beniroquai/Opentrons-Microscope-Platereader/image.png

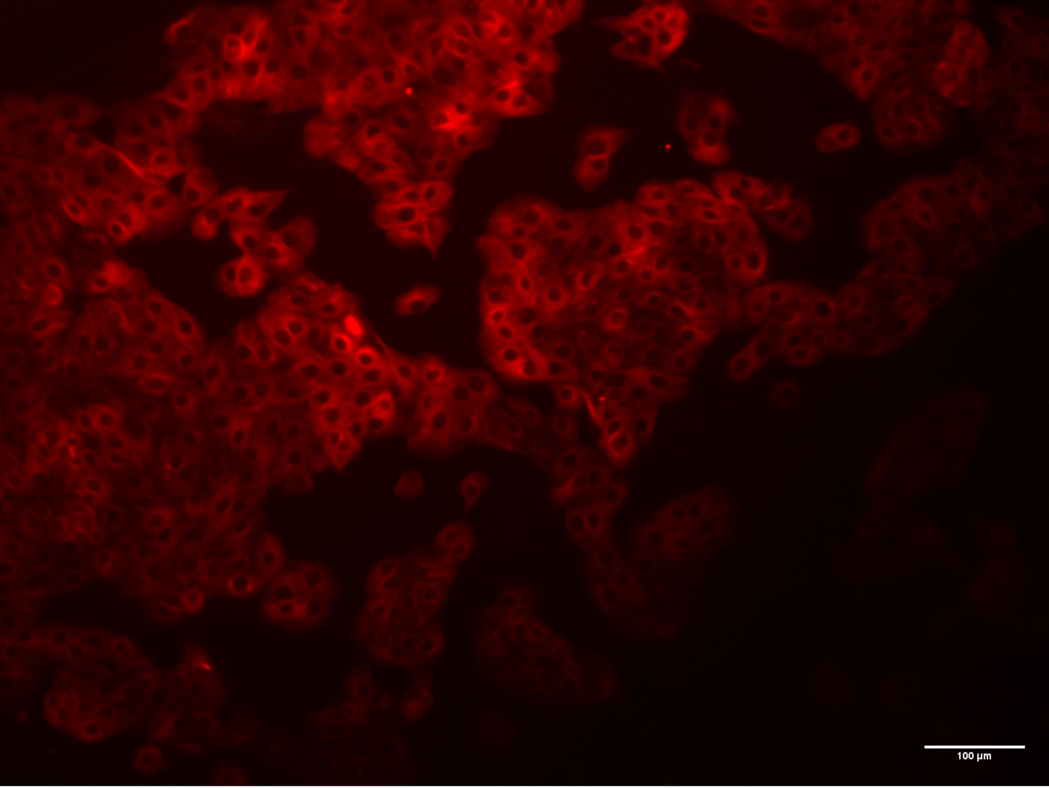
image.png
