beniroquai/Opentrons-Microscope-Platereader/IMAGES/FIG_Fluo_ring.jpg

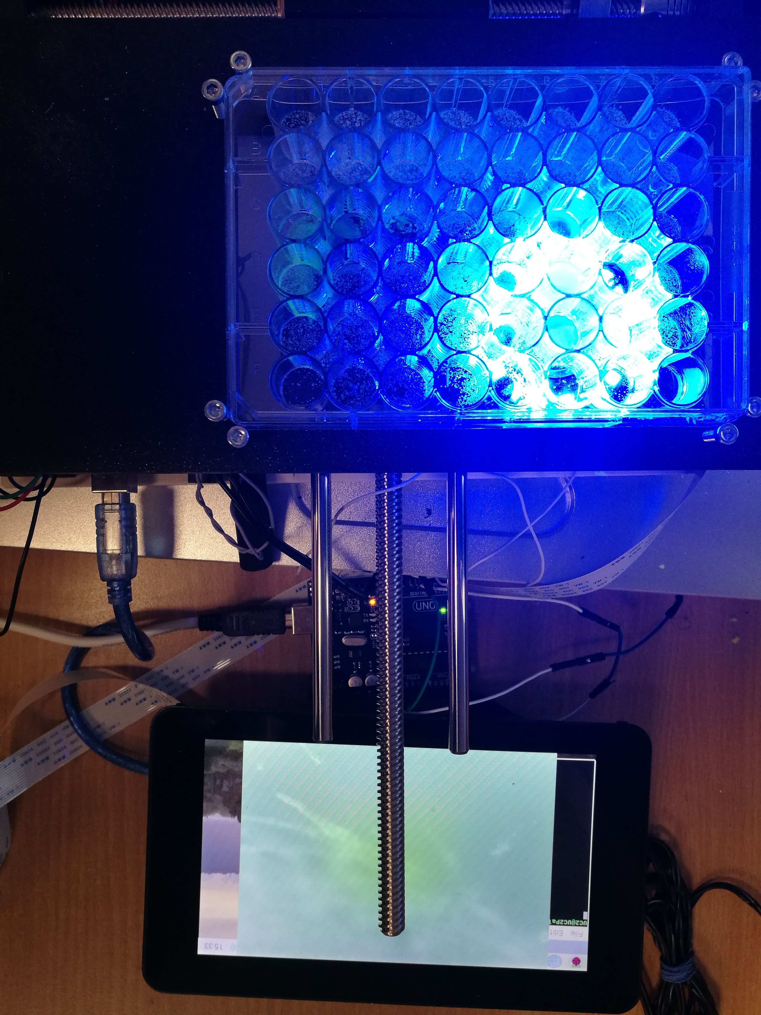
IMAGES/FIG_Fluo_ring.jpg
