beniroquai/Opentrons-Microscope-Platereader/IMAGES/laserpos.gif

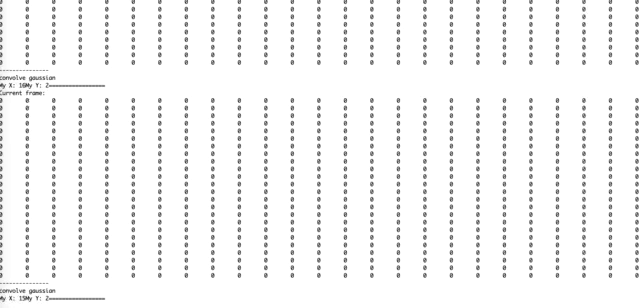
IMAGES/laserpos.gif
