beniroquai/Opentrons-Microscope-Platereader/IMAGES/Opentrons_6.jpg

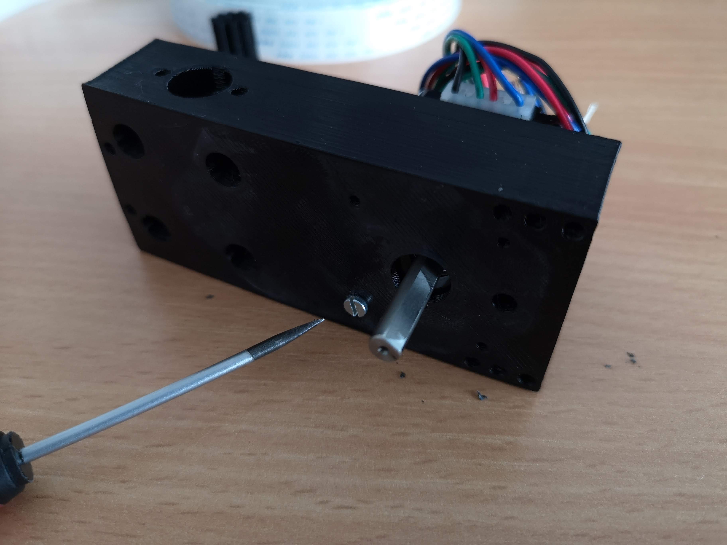
IMAGES/Opentrons_6.jpg
