beniroquai/Opentrons-Microscope-Platereader/IMAGES/Opentrons_70.jpg

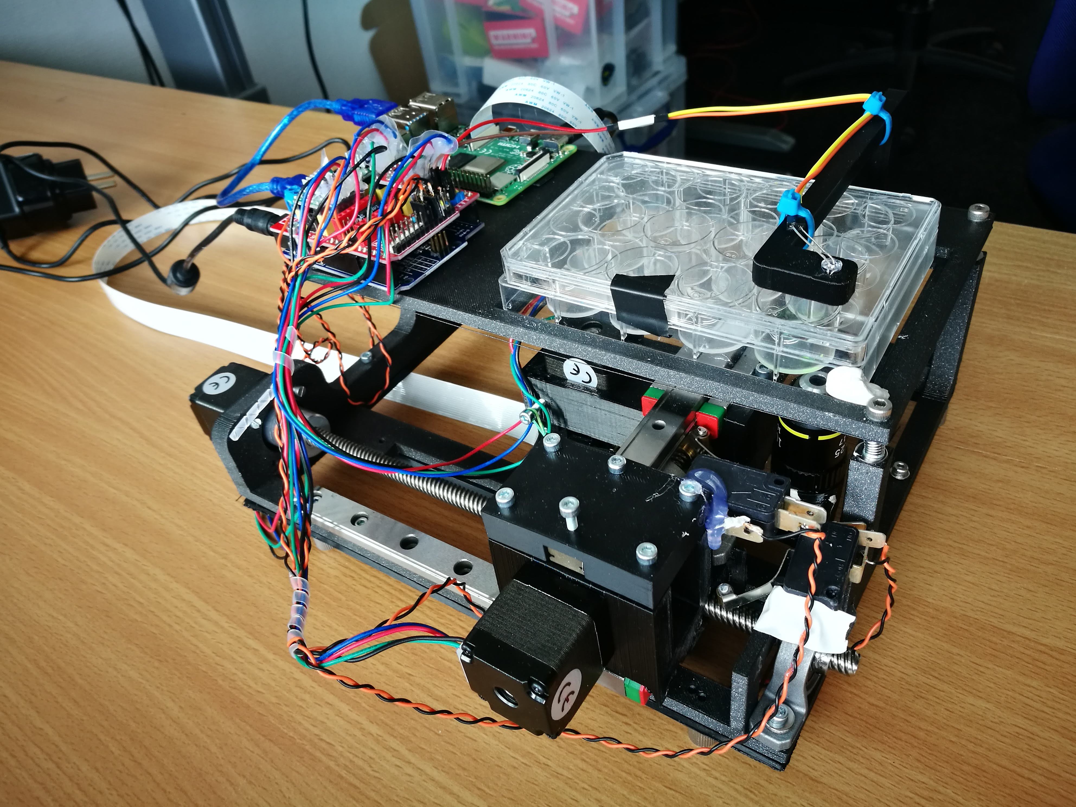
IMAGES/Opentrons_70.jpg
