beniroquai/Opentrons-Microscope-Platereader/IMAGES/Opentrons_71.jpg

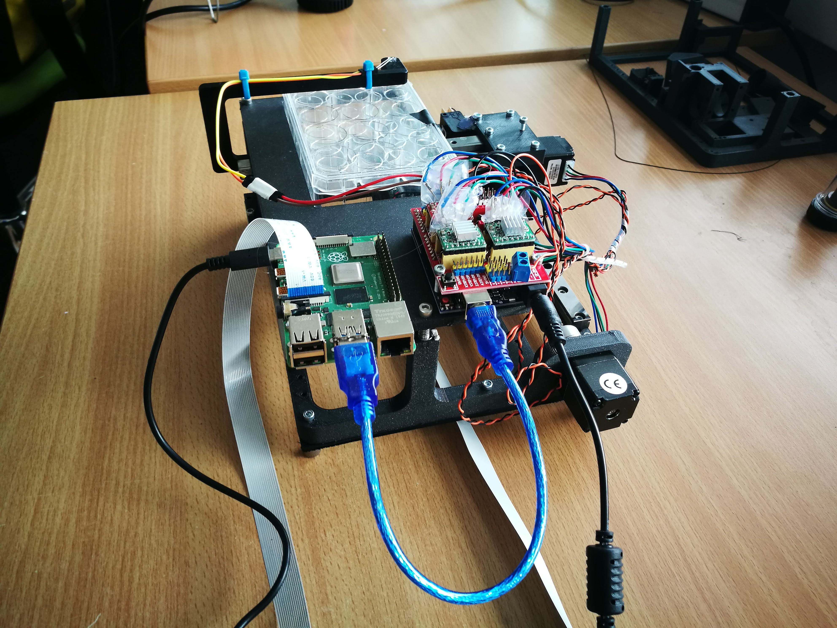
IMAGES/Opentrons_71.jpg
