beniroquai/Opentrons-Microscope-Platereader/IMAGES/Opentrons_72.jpg

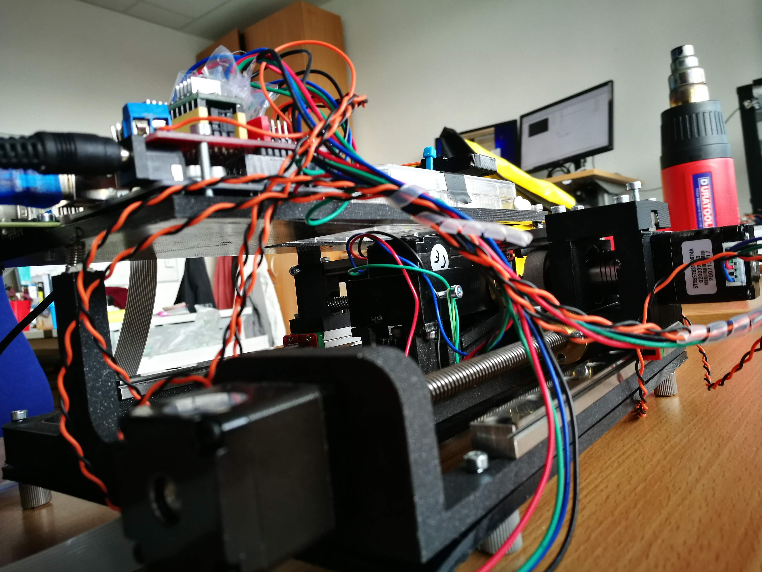
IMAGES/Opentrons_72.jpg
