beniroquai/Opentrons-Microscope-Platereader/IMAGES/Opentrons_73.jpg

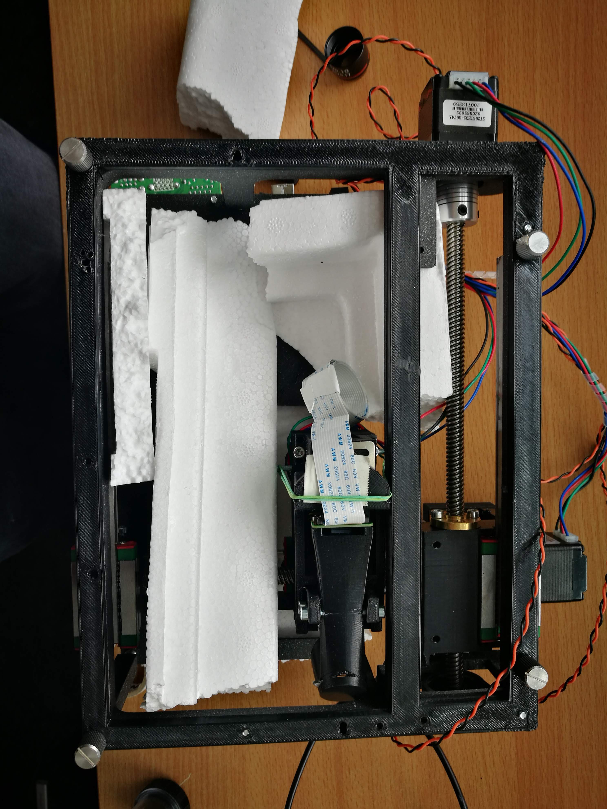
IMAGES/Opentrons_73.jpg
