beniroquai/Opentrons-Microscope-Platereader/IMAGES/Opentronsscope.png

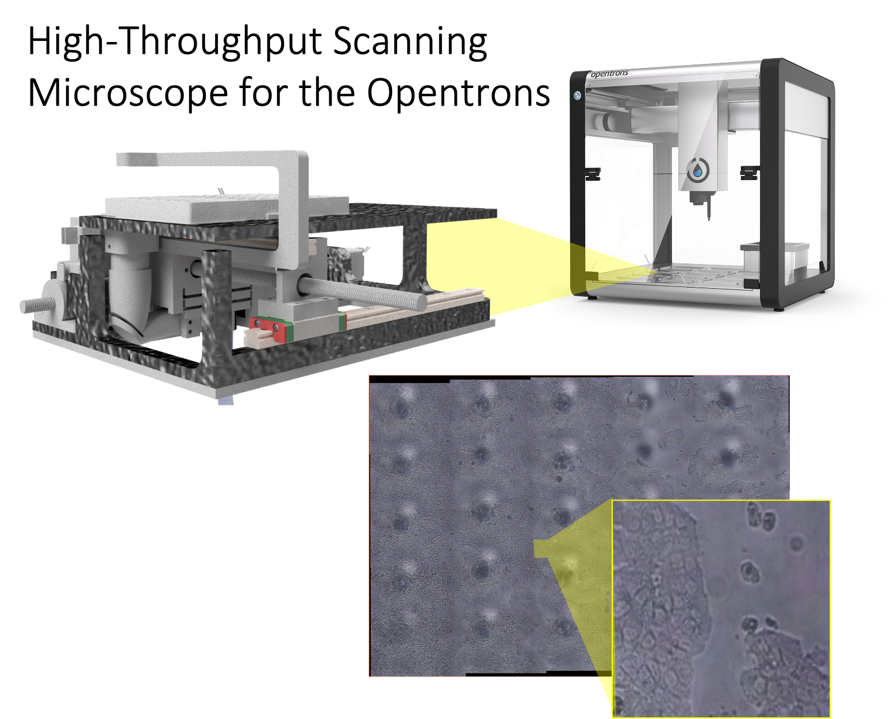
IMAGES/Opentronsscope.png
