beniroquai/Opentrons-Microscope-Platereader/IMAGES/OT_1.jpg

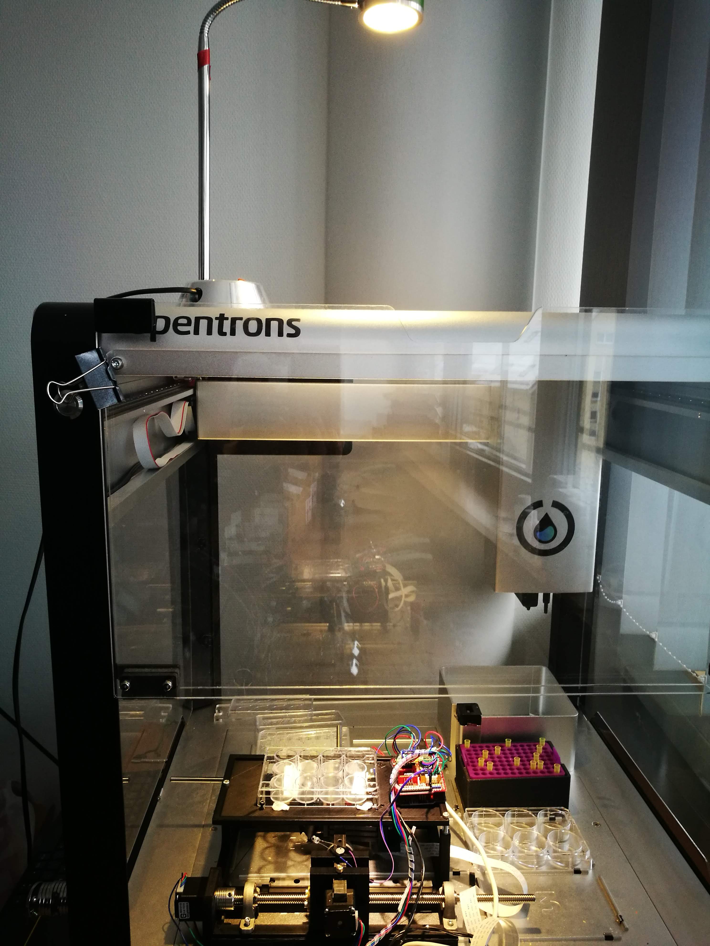
IMAGES/OT_1.jpg
