beniroquai/Opentrons-Microscope-Platereader/IMAGES/OT_2.jpg

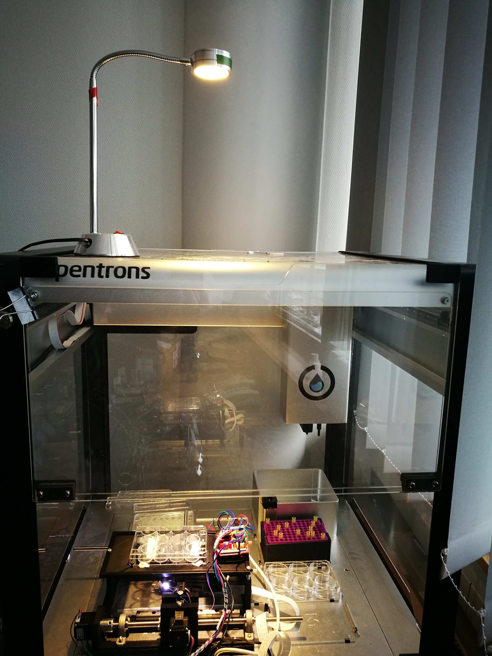
IMAGES/OT_2.jpg
