beniroquai/Opentrons-Microscope-Platereader/IMAGES/OT_3.jpg

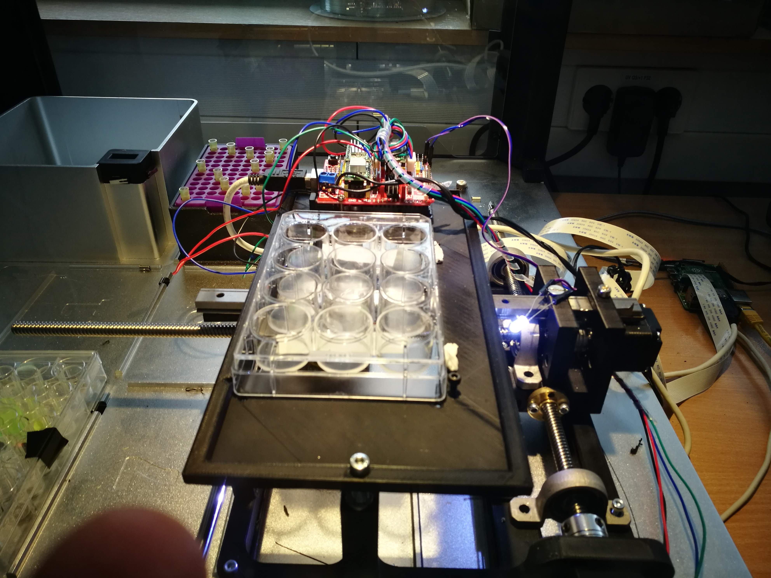
IMAGES/OT_3.jpg
