beniroquai/Opentrons-Microscope-Platereader/IMAGES/OT_4.jpg

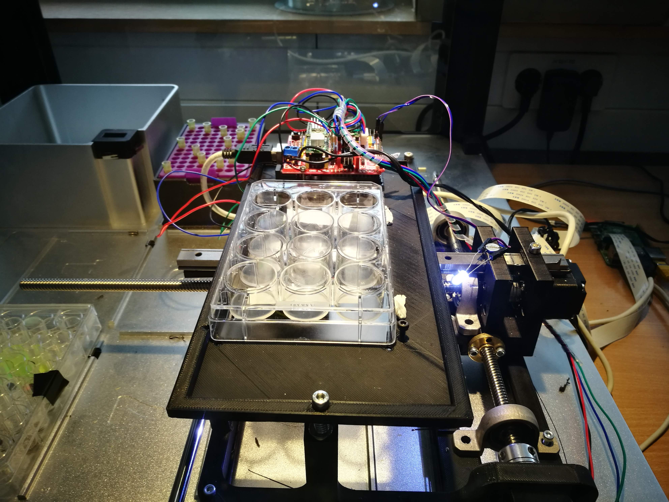
IMAGES/OT_4.jpg
