beniroquai/Opentrons-Microscope-Platereader/IMAGES/Spectrometer_Neopixel_ring_onlyBlue.PNG

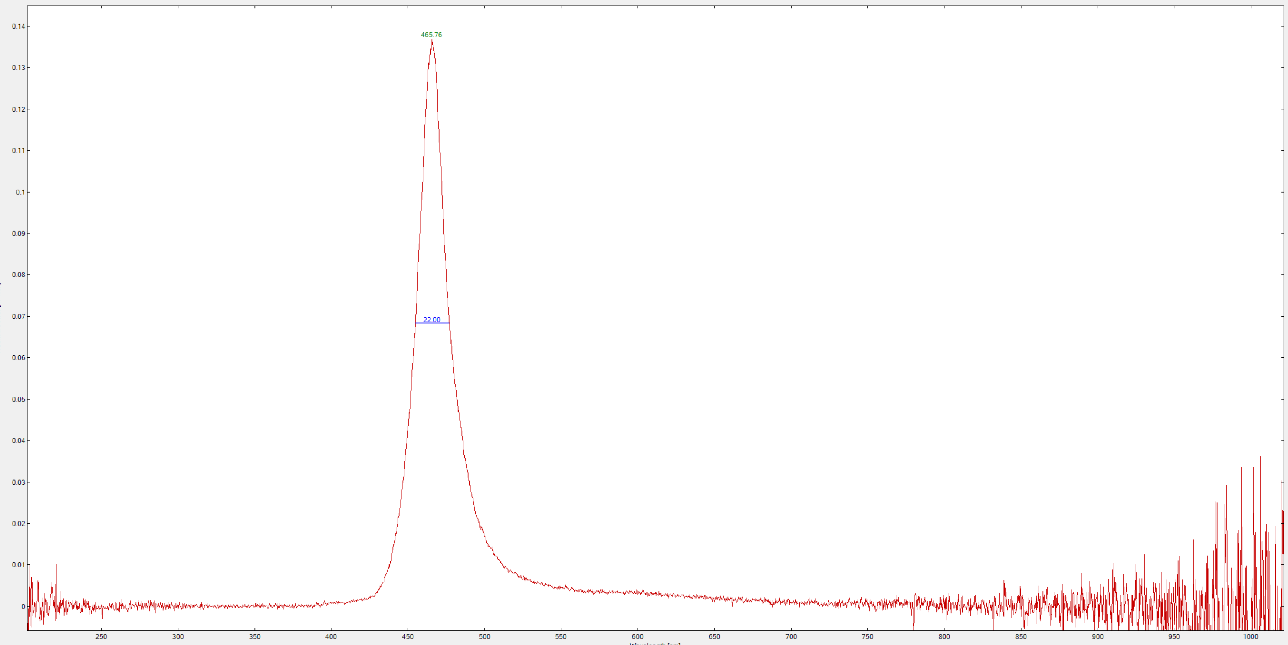
IMAGES/Spectrometer_Neopixel_ring_onlyBlue.PNG
