beniroquai/Opentrons-Microscope-Platereader/IMAGES/Stitch1.jpeg

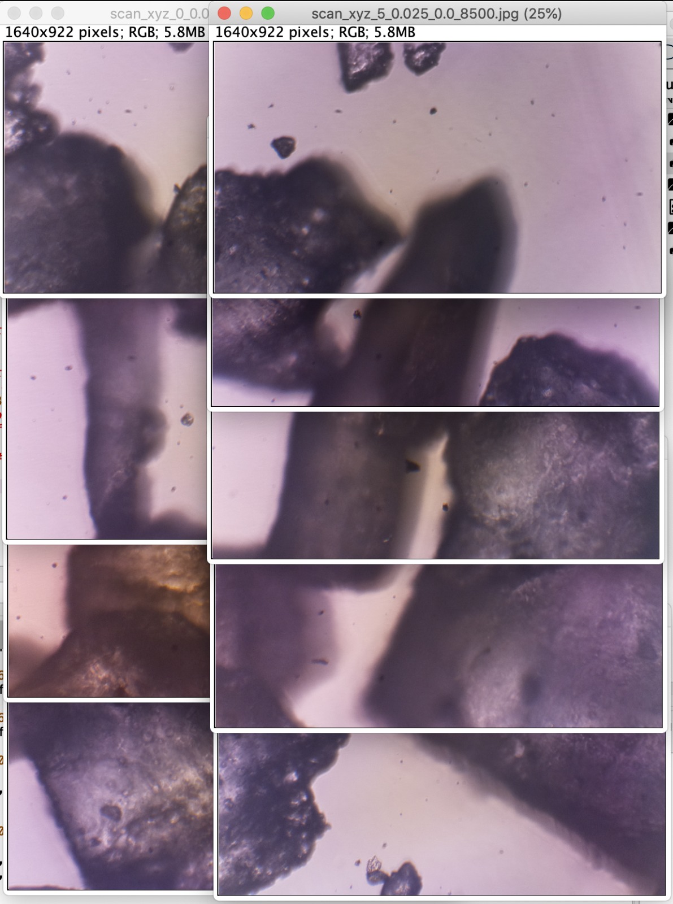
IMAGES/Stitch1.jpeg
