beniroquai/Opentrons-Microscope-Platereader/IMAGES/Z-Stack.gif

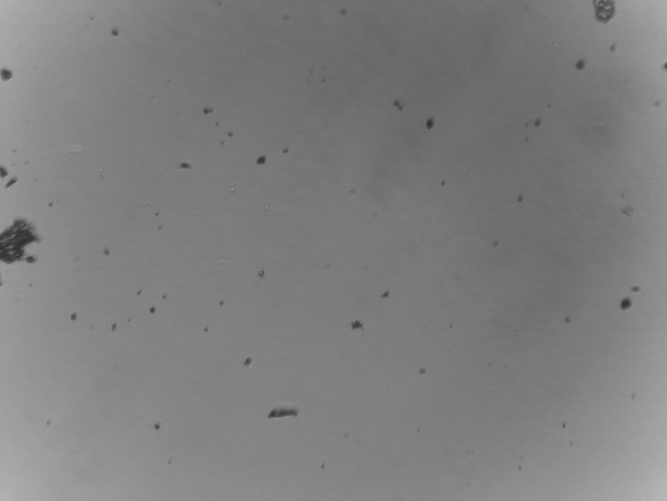
IMAGES/Z-Stack.gif
