beniroquai/Opentrons-Microscope-Platereader/INVENTOR/eppi.PNG

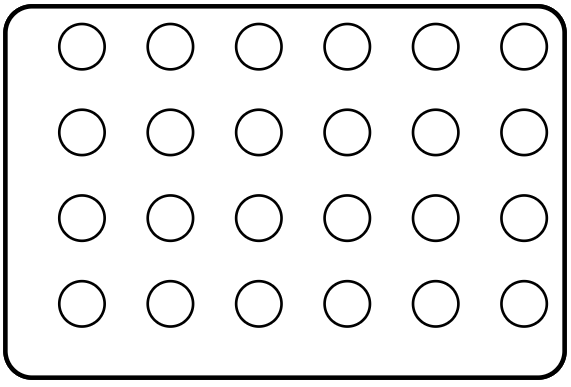
INVENTOR/eppi.PNG
