beniroquai/Opentrons-Microscope-Platereader/INVENTOR/IMG-20210314-WA0000.jpg

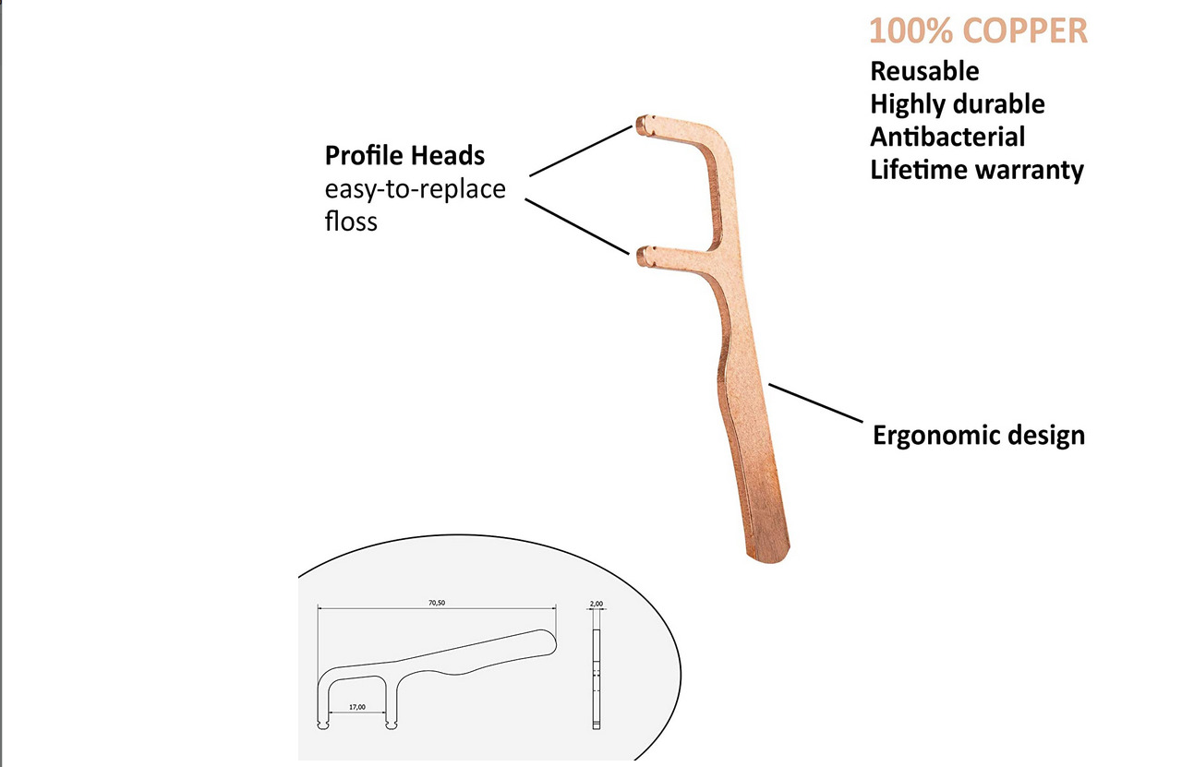
INVENTOR/IMG-20210314-WA0000.jpg
