beniroquai/Opentrons-Microscope-Platereader/PYTHON/autofocus/images/0_focussensor.png

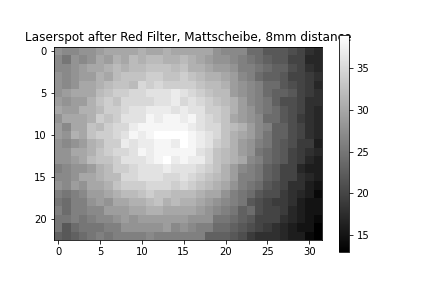
PYTHON/autofocus/images/0_focussensor.png
