beniroquai/Opentrons-Microscope-Platereader/PYTHON/autofocus/images/3_focussensor.png

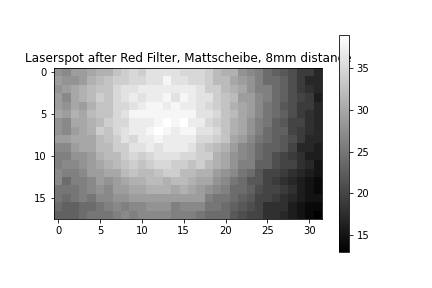
PYTHON/autofocus/images/3_focussensor.png
