beniroquai/Opentrons-Microscope-Platereader/PYTHON/autofocus/images/4_focussensor.png

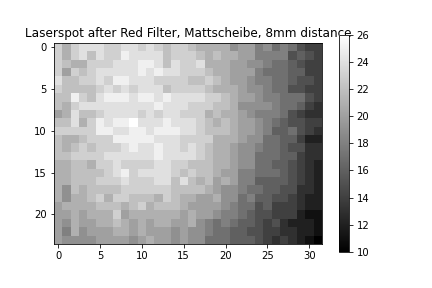
PYTHON/autofocus/images/4_focussensor.png
