beniroquai/Opentrons-Microscope-Platereader/PYTHON/autofocus/images/5_focussensor.png

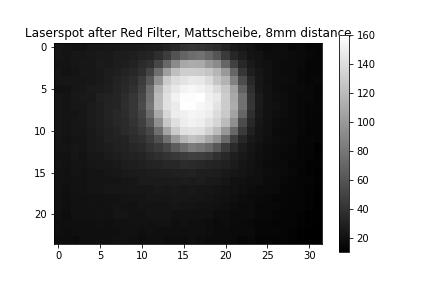
PYTHON/autofocus/images/5_focussensor.png
