beniroquai/Opentrons-Microscope-Platereader/PYTHON/autofocus/images/6_focussensor.png

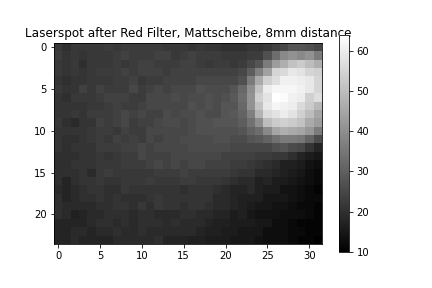
PYTHON/autofocus/images/6_focussensor.png
