beniroquai/Opentrons-Microscope-Platereader/PYTHON/autofocus/images/7_focussensor.png

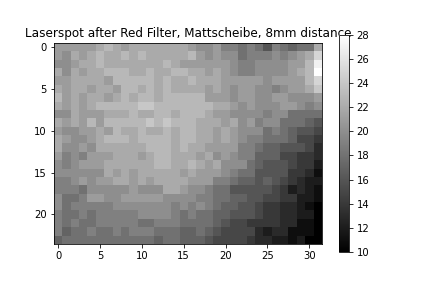
PYTHON/autofocus/images/7_focussensor.png
