beniroquai/Opentrons-Microscope-Platereader/PYTHON/autofocus/images/8_focussensor.png

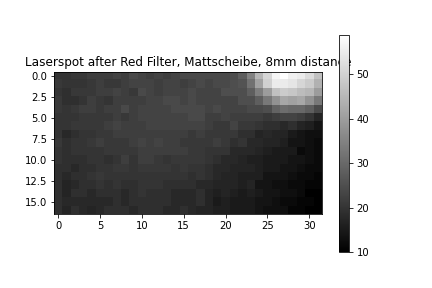
PYTHON/autofocus/images/8_focussensor.png
