beniroquai/Opentrons-Microscope-Platereader/PYTHON/autofocus/images/9_focussensor.png

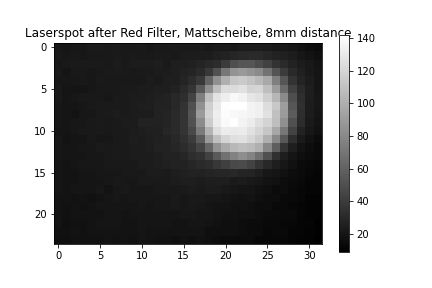
PYTHON/autofocus/images/9_focussensor.png
