beniroquai/Opentrons-Microscope-Platereader/PYTHON/autofocus/images/11_focussensor.png

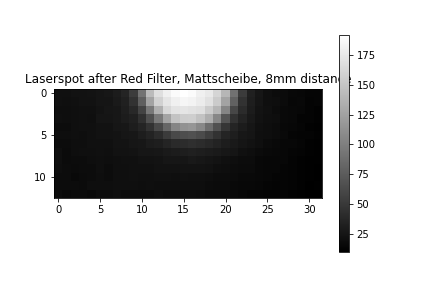
PYTHON/autofocus/images/11_focussensor.png
