beniroquai/Opentrons-Microscope-Platereader/PYTHON/autofocus/images/12_focussensor.png

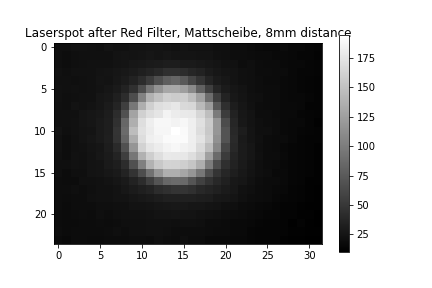
PYTHON/autofocus/images/12_focussensor.png
