beniroquai/Opentrons-Microscope-Platereader/PYTHON/autofocus/images/15_focussensor.png

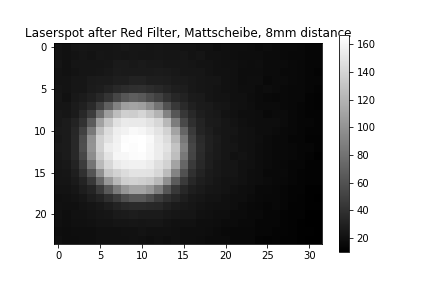
PYTHON/autofocus/images/15_focussensor.png
