beniroquai/Opentrons-Microscope-Platereader/PYTHON/autofocus/images/20_focussensor.png

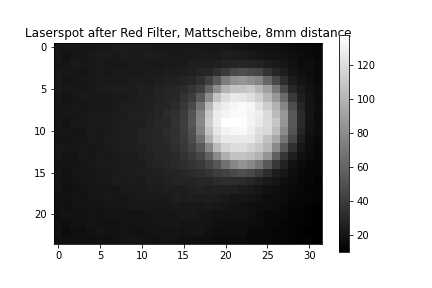
PYTHON/autofocus/images/20_focussensor.png
