beniroquai/Opentrons-Microscope-Platereader/PYTHON/autofocus/images/Neuer Ordner mit Objekten/0_focussensor.png

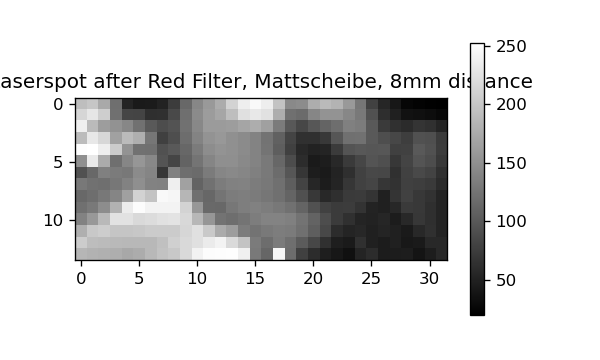
PYTHON/autofocus/images/Neuer Ordner mit Objekten/0_focussensor.png
