beniroquai/Opentrons-Microscope-Platereader/PYTHON/autofocus/images/Neuer Ordner mit Objekten/26_focussensor.png

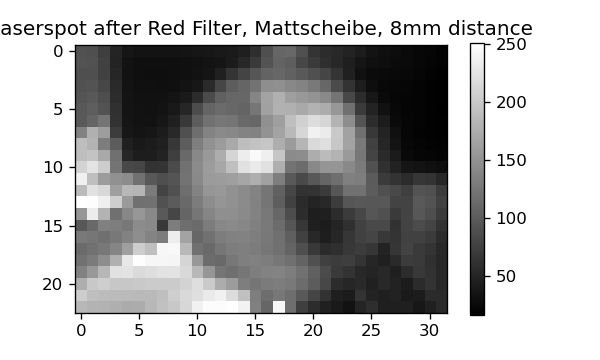
PYTHON/autofocus/images/Neuer Ordner mit Objekten/26_focussensor.png
