beniroquai/Opentrons-Microscope-Platereader/PYTHON/autofocus/images/Neuer Ordner mit Objekten/27_focussensor.png

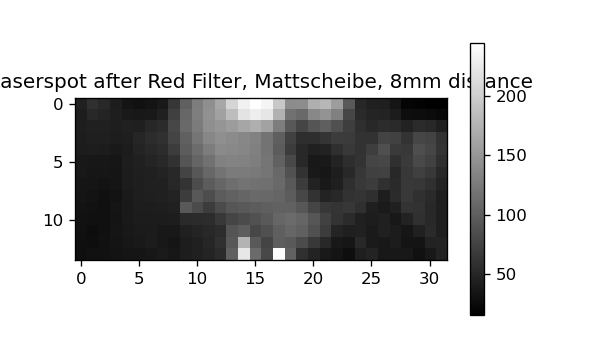
PYTHON/autofocus/images/Neuer Ordner mit Objekten/27_focussensor.png
