beniroquai/Opentrons-Microscope-Platereader/PYTHON/autofocus/images/Neuer Ordner mit Objekten/29_focussensor.png

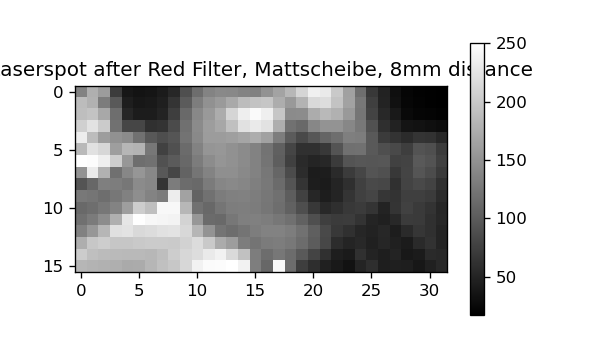
PYTHON/autofocus/images/Neuer Ordner mit Objekten/29_focussensor.png
