beniroquai/Opentrons-Microscope-Platereader/PYTHON/autofocus/images/Neuer Ordner mit Objekten/46_focussensor.png

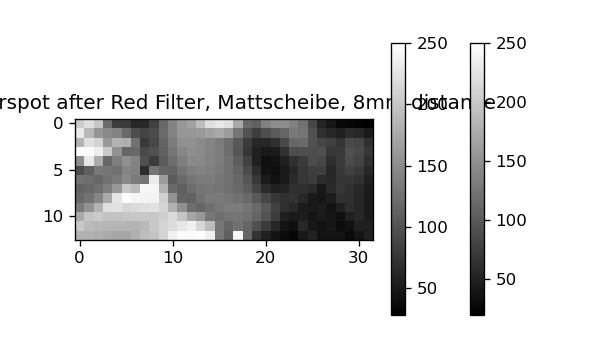
PYTHON/autofocus/images/Neuer Ordner mit Objekten/46_focussensor.png
