beniroquai/Opentrons-Microscope-Platereader/PYTHON/myautofocus.png

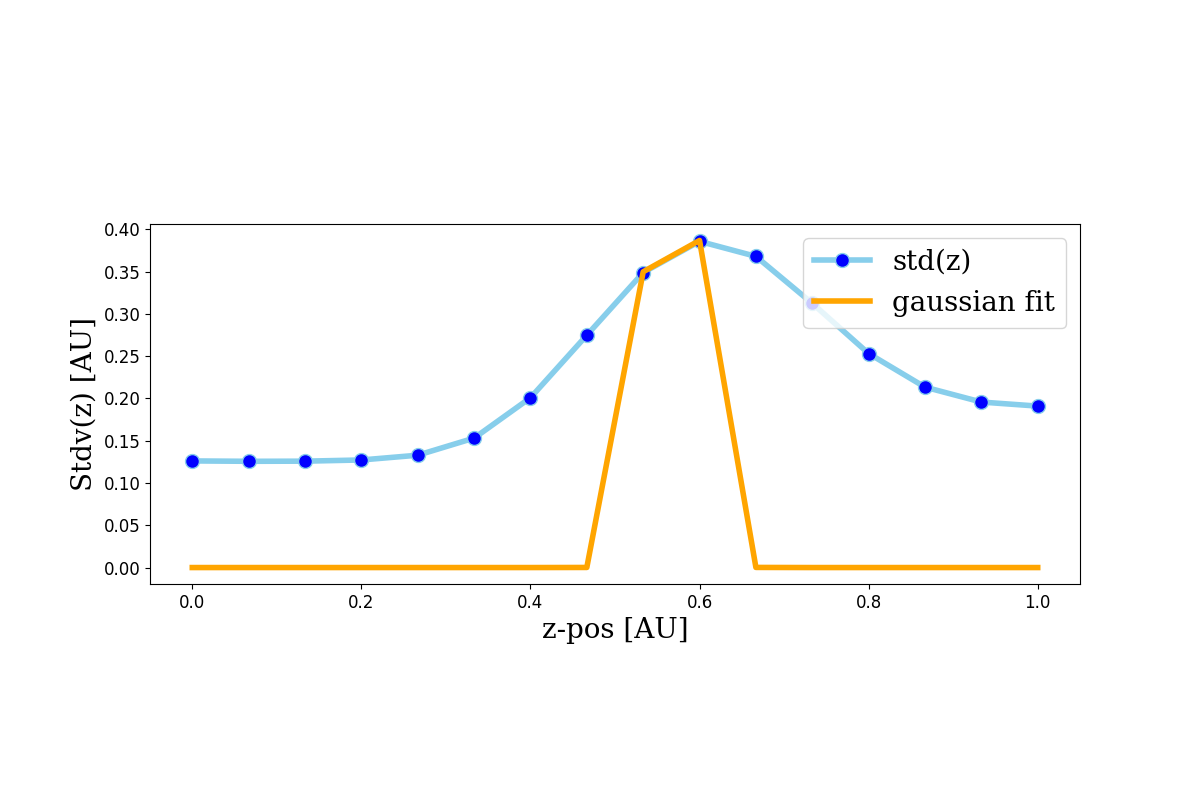
PYTHON/myautofocus.png
