beniroquai/Opentrons-Microscope-Platereader/PYTHON/scan_2020-11-08_16-35-54/scan_xyz_0_0.0_0.0_8500.jpg

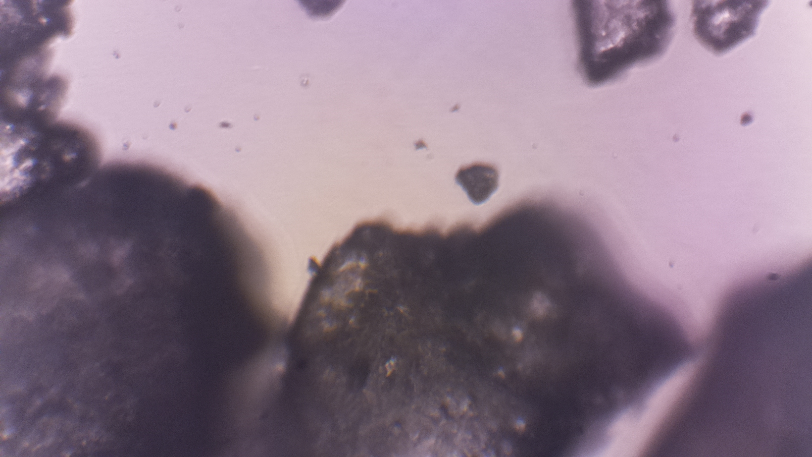
PYTHON/scan_2020-11-08_16-35-54/scan_xyz_0_0.0_0.0_8500.jpg
