beniroquai/Opentrons-Microscope-Platereader/PYTHON/scan_2020-11-08_16-35-54/scan_xyz_10_0.05_0.0_8500.jpg

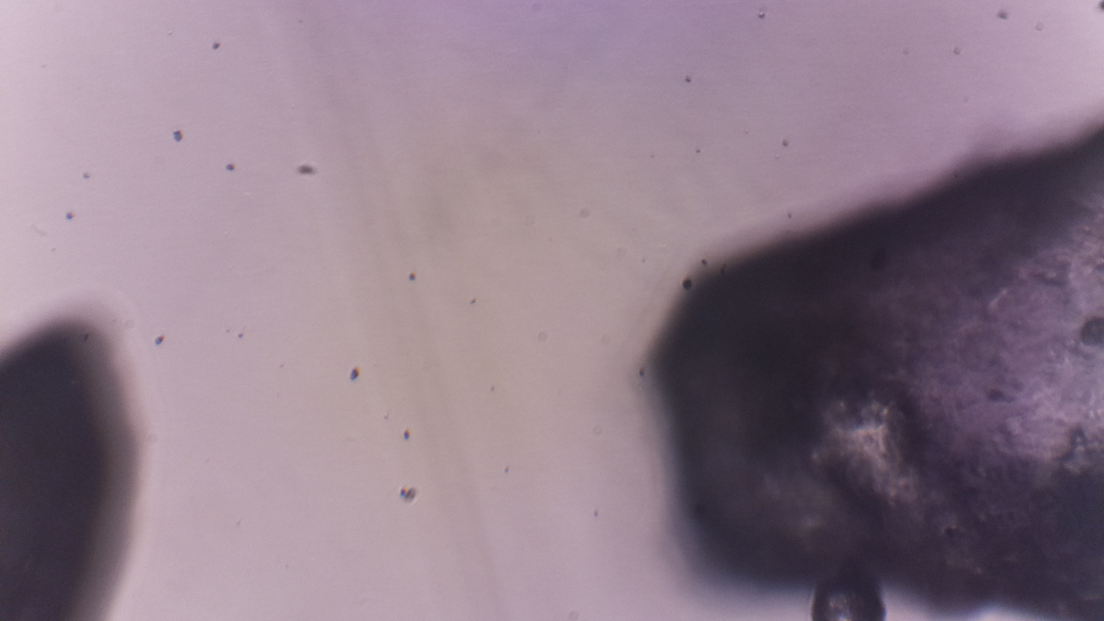
PYTHON/scan_2020-11-08_16-35-54/scan_xyz_10_0.05_0.0_8500.jpg
