beniroquai/Opentrons-Microscope-Platereader/PYTHON/scan_2020-11-08_16-35-54/scan_xyz_11_0.05_0.02_8500.jpg

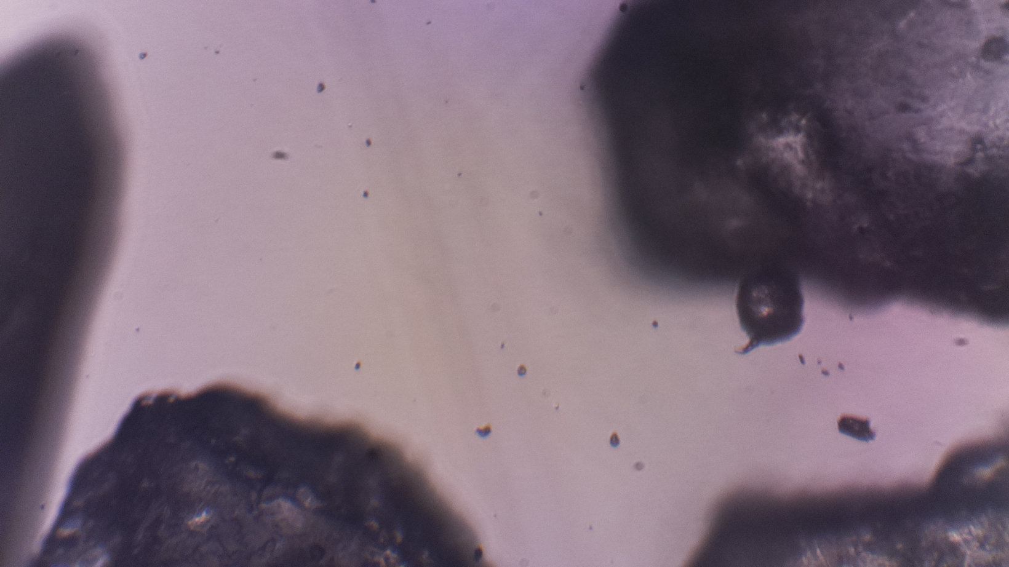
PYTHON/scan_2020-11-08_16-35-54/scan_xyz_11_0.05_0.02_8500.jpg
