beniroquai/Opentrons-Microscope-Platereader/PYTHON/scan_2020-11-08_16-35-54/scan_xyz_19_0.07500000000000001_0.08_8500.jpg

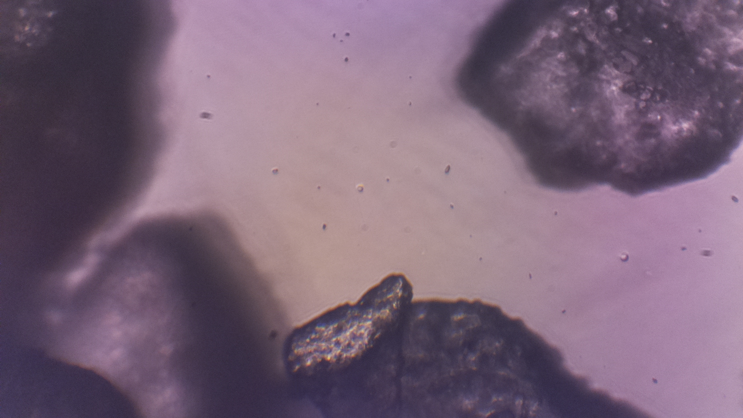
PYTHON/scan_2020-11-08_16-35-54/scan_xyz_19_0.07500000000000001_0.08_8500.jpg
