beniroquai/Opentrons-Microscope-Platereader/PYTHON/scan_2020-11-08_16-35-54/scan_xyz_21_0.1_0.02_8500.jpg

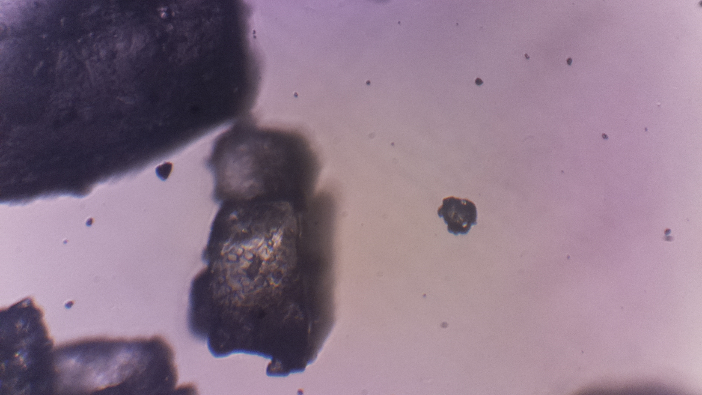
PYTHON/scan_2020-11-08_16-35-54/scan_xyz_21_0.1_0.02_8500.jpg
