beniroquai/Opentrons-Microscope-Platereader/SCAN_2021-04-21_10-45-28.tif kept stack - drift corrected-4_rareevent.gif

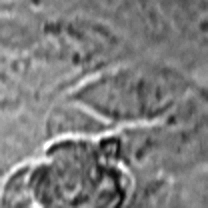
SCAN_2021-04-21_10-45-28.tif kept stack - drift corrected-4_rareevent.gif
