beniroquai/Opentrons-Microscope-Platereader/INVENTOR/09_Lid_Electronics.stl

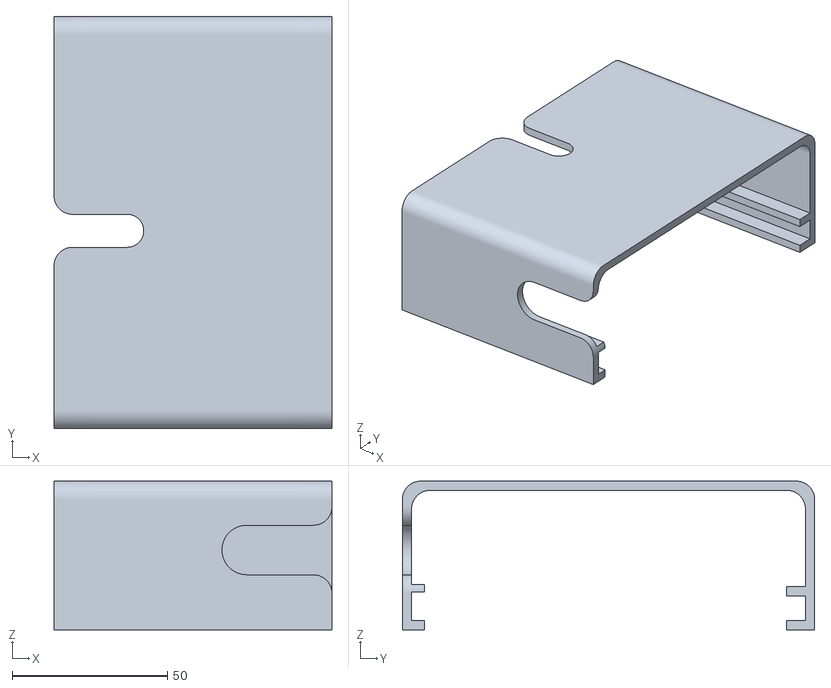
[picture p80: CAD file, 2021-03-26]
INVENTOR/09_Lid_Electronics.stl
89.6 x 133.0 x 48.0
