beniroquai/Opentrons-Microscope-Platereader/STL/Opentronscope_01_Slide_camera_v1.stl

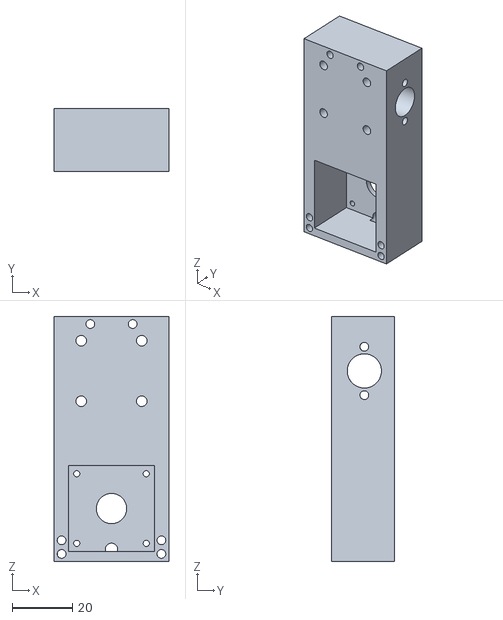
[picture p81: CAD file, 2021-03-16]
STL/Opentronscope_01_Slide_camera_v1.stl
38.0 x 20.9 x 81.0
