beniroquai/Opentrons-Microscope-Platereader/INVENTOR/09_Opentrons_Microscope_Baseplate.stl

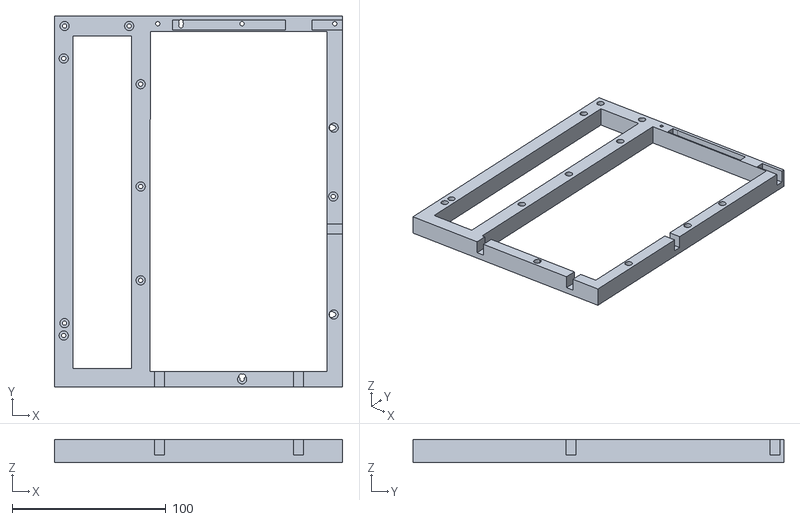
[picture p82: CAD file, 2021-03-26]
INVENTOR/09_Opentrons_Microscope_Baseplate.stl
187.1 x 241.0 x 15.0
