beniroquai/Opentrons-Microscope-Platereader/STL/Opentronscope_01_Slide_camera_flexure_v1.stl

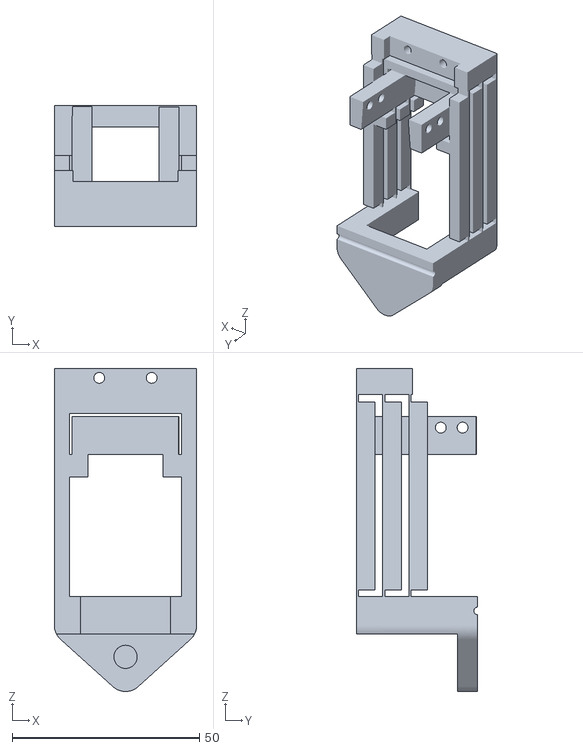
[picture p83: CAD file, 2021-03-16]
STL/Opentronscope_01_Slide_camera_flexure_v1.stl
38.0 x 32.4 x 86.3
