beniroquai/Opentrons-Microscope-Platereader/INVENTOR/OT-2 Reference Model Basic.STEP

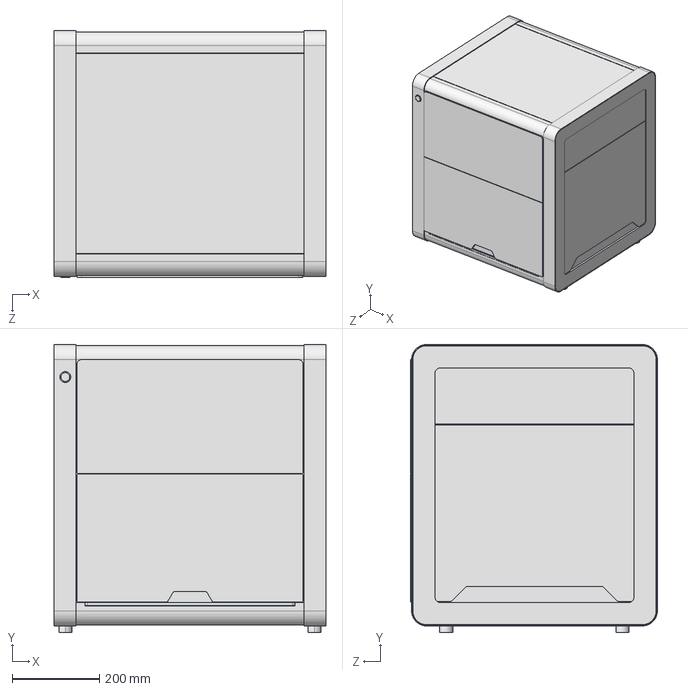
[picture p84: CAD file, 2021-03-26]
INVENTOR/OT-2 Reference Model Basic.STEP
624.3 x 662.0 x 567.4 mm
