beniroquai/Opentrons-Microscope-Platereader/STL/Opentronscope_opentrons_gear1.stl

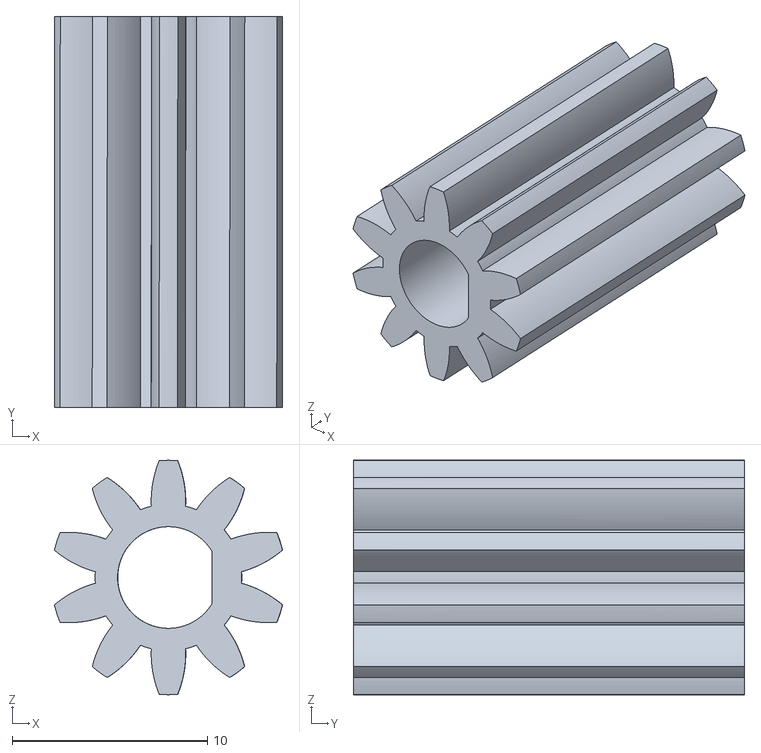
[picture p85: CAD file, 2021-03-16]
STL/Opentronscope_opentrons_gear1.stl
11.7 x 20.0 x 12.0
