beniroquai/Opentrons-Microscope-Platereader/INVENTOR/OT-2 Reference Model Detailed.STEP

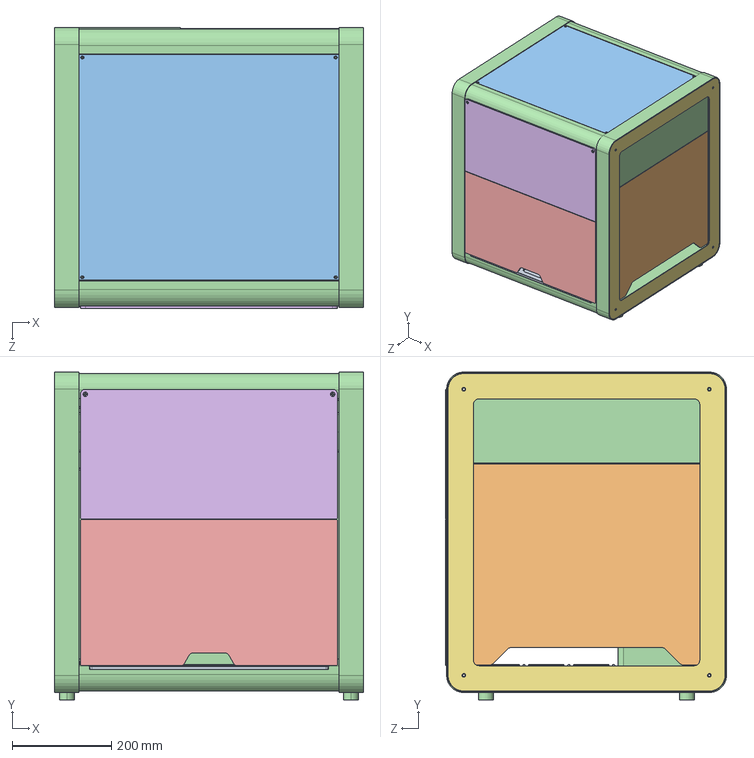
[picture p86: CAD file, 2021-03-26]
INVENTOR/OT-2 Reference Model Detailed.STEP
624.3 x 662.0 x 567.5 mm
