beniroquai/Opentrons-Microscope-Platereader/STL/Opentronscope_01_opticsmodule.stl

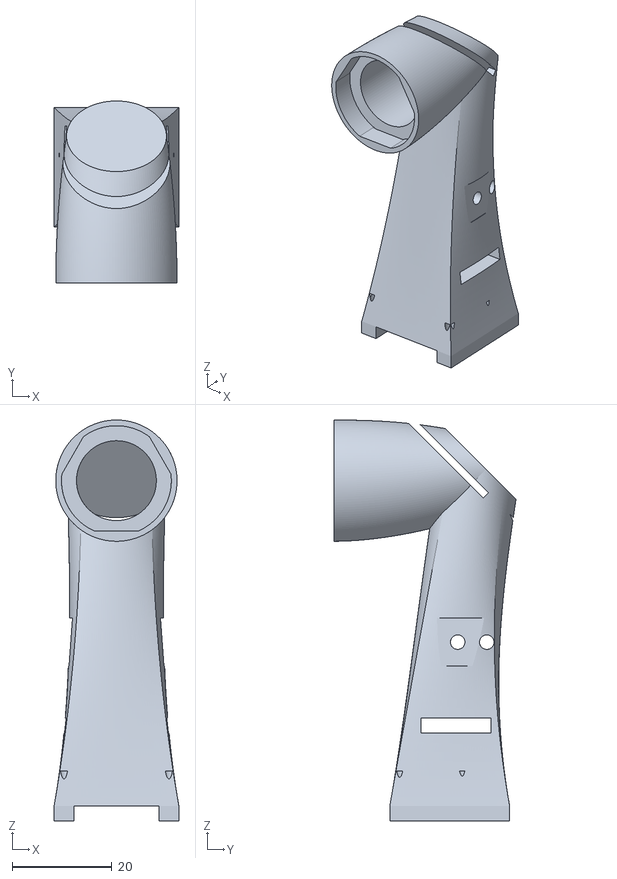
[picture p87: CAD file, 2021-03-16]
STL/Opentronscope_01_opticsmodule.stl
25.0 x 36.5 x 80.3
