beniroquai/Opentrons-Microscope-Platereader/INVENTOR/00_endstop_optical.stp

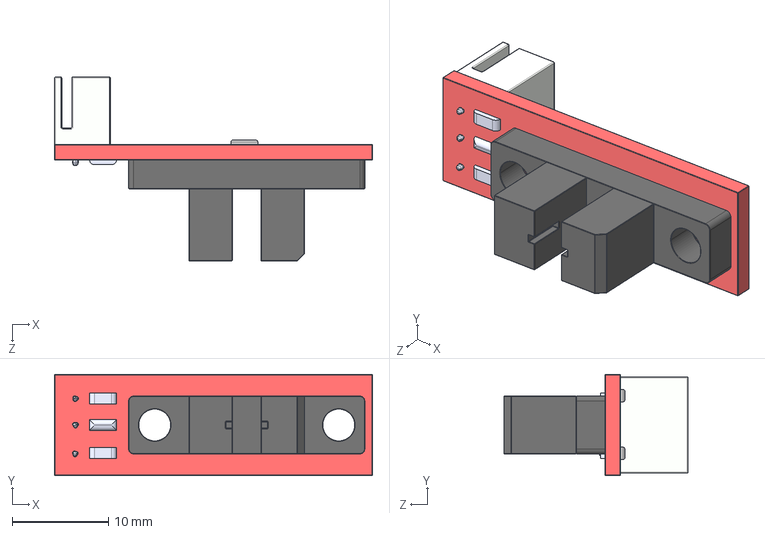
[picture p88: CAD file, 2021-03-06]
INVENTOR/00_endstop_optical.stp
33.0 x 10.5 x 19.1 mm
