beniroquai/Opentrons-Microscope-Platereader/STL/Opentronscope_03_Support_Xslide.stl

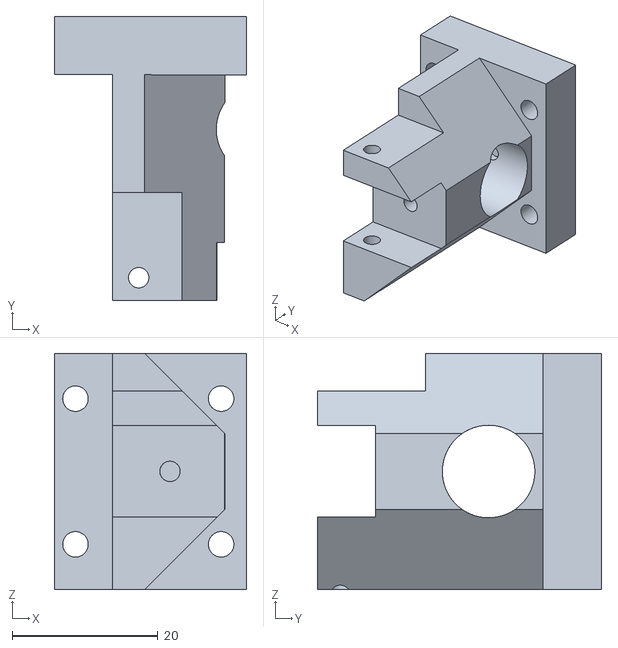
[picture p89: CAD file, 2021-03-16]
STL/Opentronscope_03_Support_Xslide.stl
26.4 x 39.0 x 32.4
