beniroquai/Opentrons-Microscope-Platereader/STL/Opentronscope_10_OPENTRONS_LED_FLUO_MODULE.stl

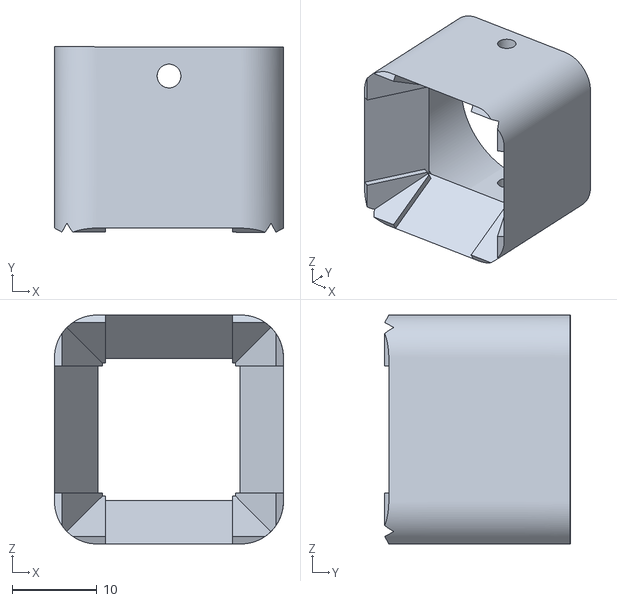
[picture p90: CAD file, 2021-03-16]
STL/Opentronscope_10_OPENTRONS_LED_FLUO_MODULE.stl
27.0 x 21.9 x 27.0
