beniroquai/Opentrons-Microscope-Platereader/STL/Opentronscope_09_Opentrons_Microscope_Baseplate.stl

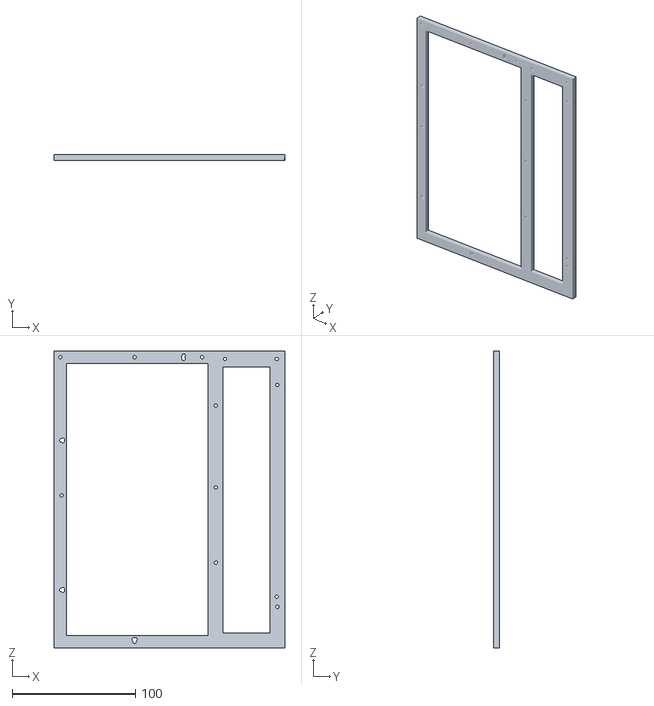
[picture p91: CAD file, 2021-03-16]
STL/Opentronscope_09_Opentrons_Microscope_Baseplate.stl
187.1 x 5.10 x 241.0
