beniroquai/Opentrons-Microscope-Platereader/INVENTOR/Assembly_Opentrons_Imagingunit_v3.png

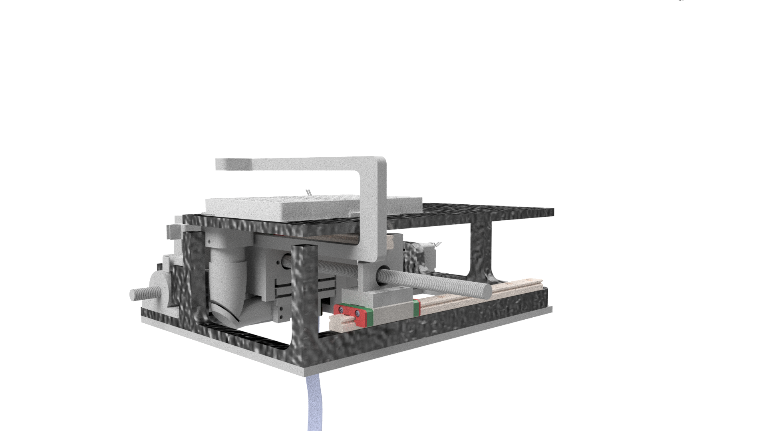
INVENTOR/Assembly_Opentrons_Imagingunit_v3.png
