beniroquai/Opentrons-Microscope-Platereader/IMAGES/StitchResultHela.jpeg

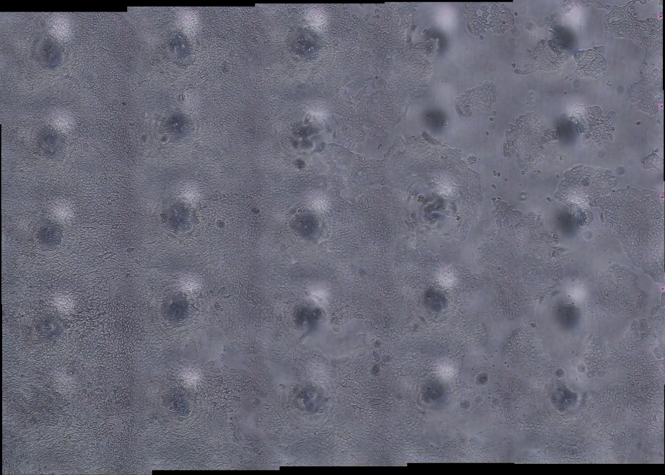
IMAGES/StitchResultHela.jpeg
