beniroquai/Opentrons-Microscope-Platereader/PYTHON/opentrons_serialmonitor.py

#!/usr/bin/env python3
# -*- coding: utf-8 -*-
"""
Created on Sat Dec  5 14:59:11 2020

@author: bene
"""
import serial
import time
import xystepper as xy
import picamera
import numpy as np

# Initiliaze Focussensor
ser = serial.Serial("/dev/ttyUSB1", 115200, bytesize=8, stopbits=serial.STOPBITS_ONE, parity=serial.PARITY_NONE)
ser.flushInput()

while(1):
    # Read the focus value
    ser_bytes = ser.readline()
    decoded_bytes = (ser_bytes[0:len(ser_bytes)-2].decode("utf-8"))
    focuspos = int(decoded_bytes.split("pos: ")[-1])
    focusval = int(decoded_bytes.split("Val: ")[-1].split(" at")[0])
    print(ser_bytes)
    print("focusval: "+str(focusval))
